Tacot2009/WETI-2025_26-Szymon_Filipkowski/.no-git_prezentacja/adc/496627323_1738310480376580_9046649333481038112_n.jpg

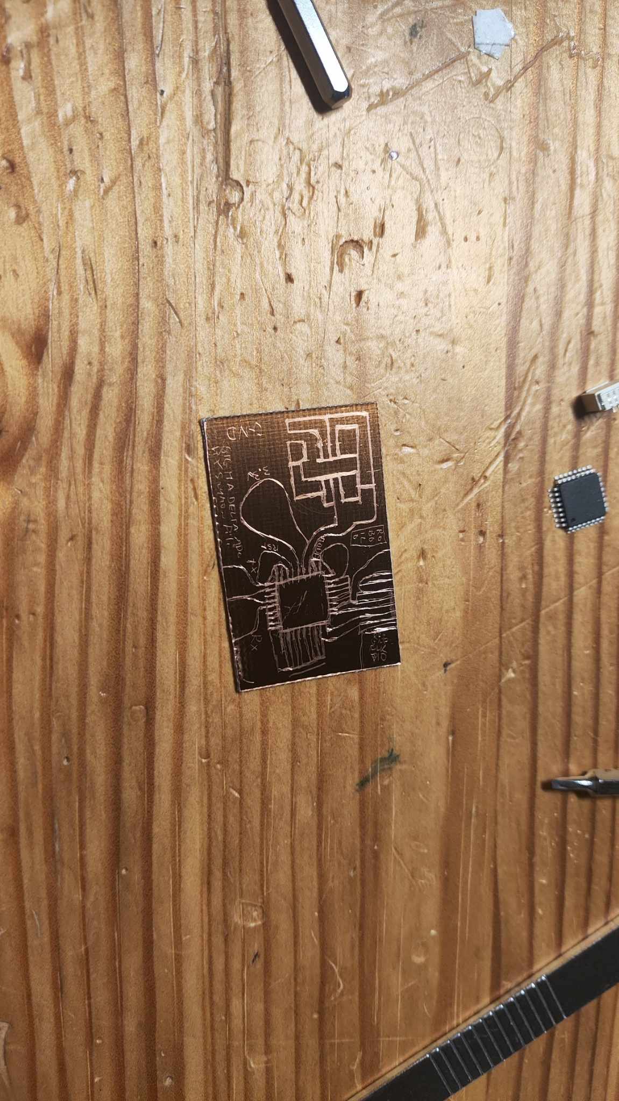
.no-git_prezentacja/adc/496627323_1738310480376580_9046649333481038112_n.jpg
