Tacot2009/WETI-2025_26-Szymon_Filipkowski/.no-git_prezentacja/adc/503926375_3727567250866873_8465031309394461046_n.jpg

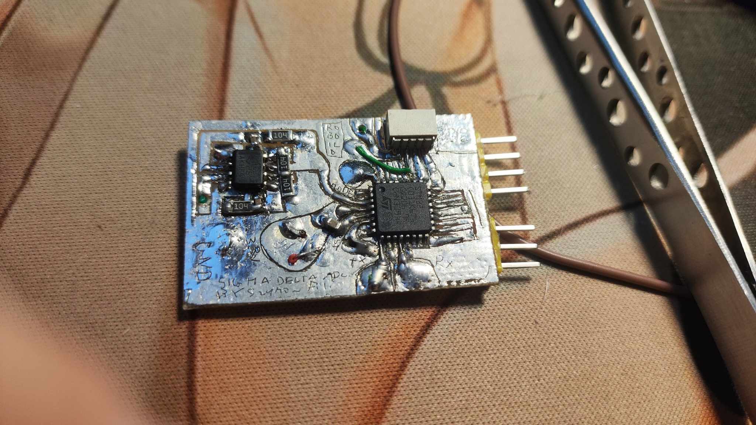
.no-git_prezentacja/adc/503926375_3727567250866873_8465031309394461046_n.jpg
