Tacot2009/WETI-2025_26-Szymon_Filipkowski/.no-git_prezentacja/adc/IMG_20250626_213812.jpg

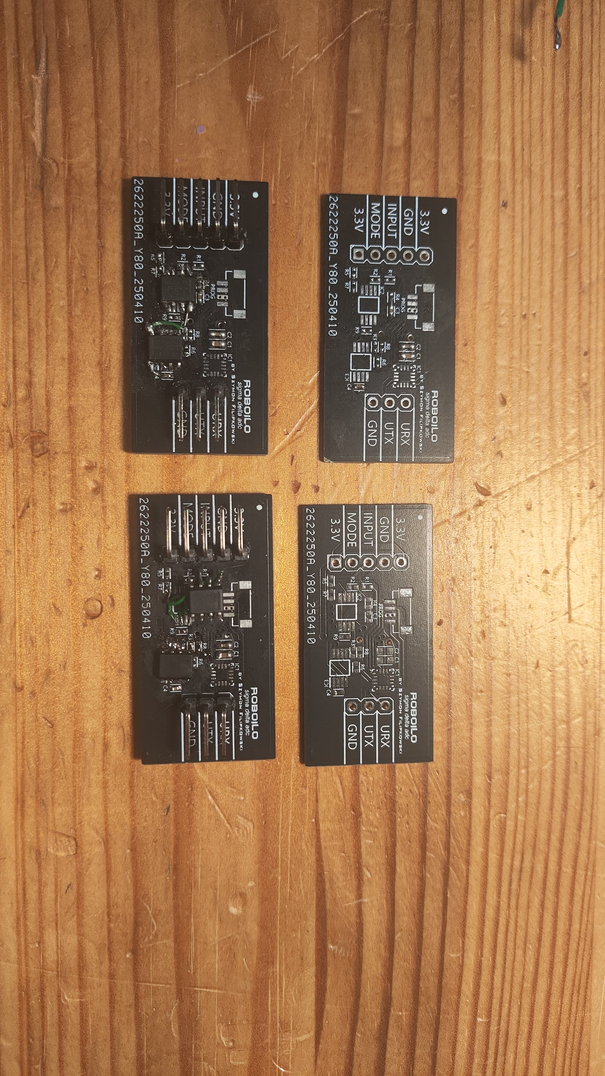
.no-git_prezentacja/adc/IMG_20250626_213812.jpg
