Tacot2009/WETI-2025_26-Szymon_Filipkowski/.no-git_prezentacja/adc/Screenshot 2025-06-26 221227.png

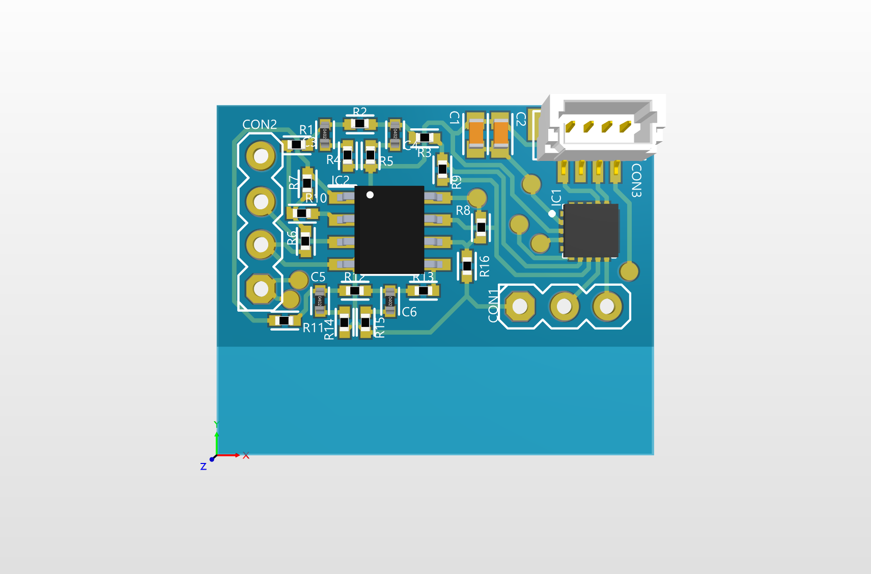
.no-git_prezentacja/adc/Screenshot 2025-06-26 221227.png
