Tacot2009/WETI-2025_26-Szymon_Filipkowski/.no-git_prezentacja/IMG_20250225_163824.jpg

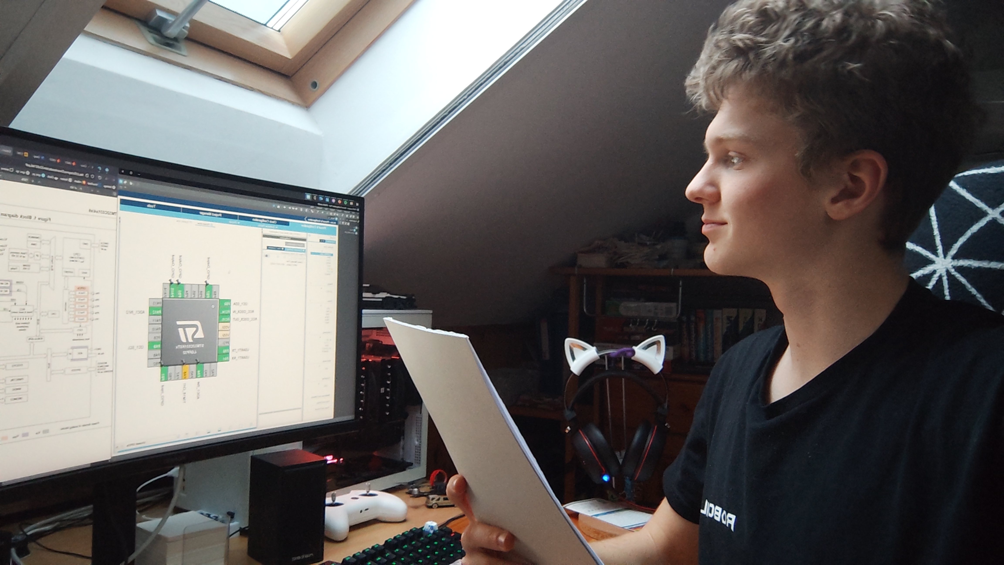
.no-git_prezentacja/IMG_20250225_163824.jpg
