Tacot2009/WETI-2025_26-Szymon_Filipkowski/.no-git_prezentacja/scheme z wartosciami.png

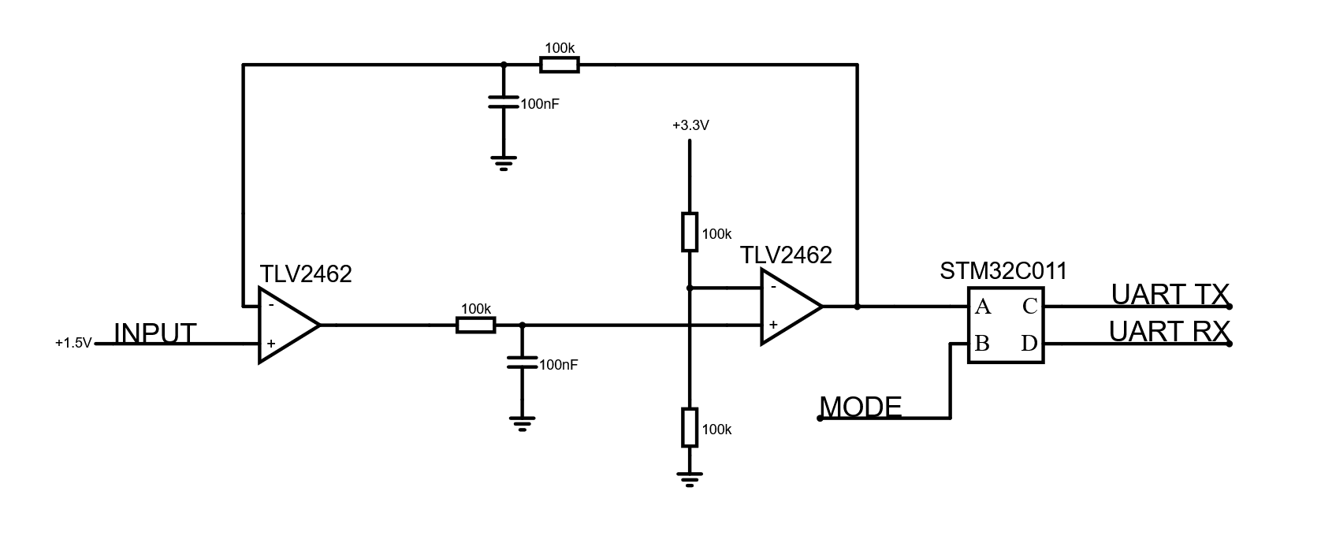
.no-git_prezentacja/scheme z wartosciami.png
