Tacot2009/WETI-2025_26-Szymon_Filipkowski/.no-git_prezentacja/Screenshot 2025-06-26 2114249.png

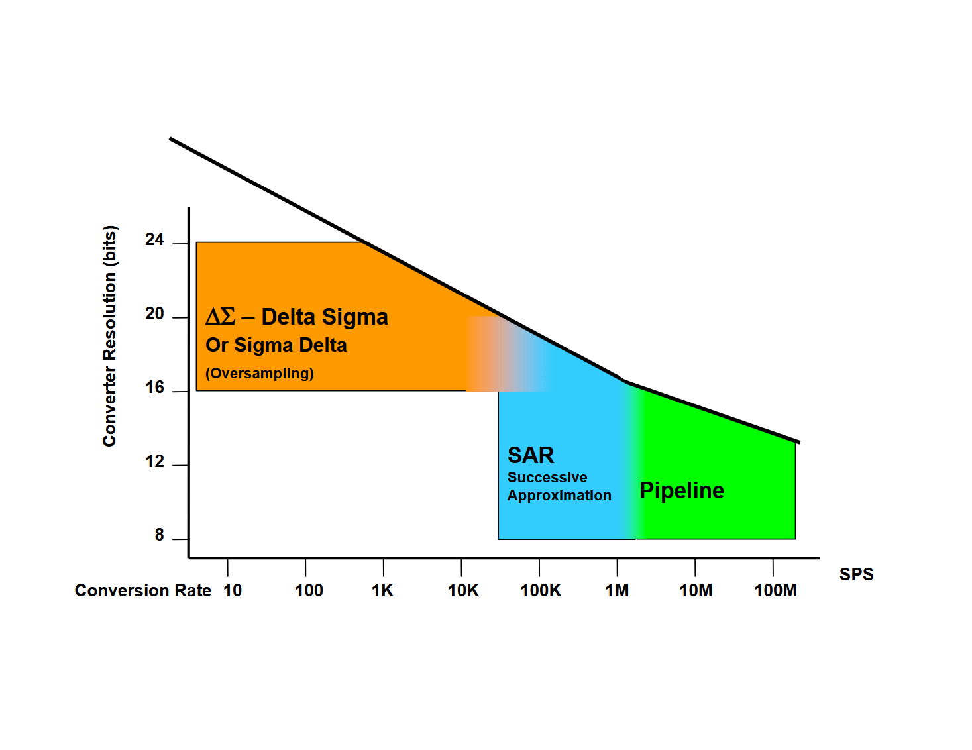
.no-git_prezentacja/Screenshot 2025-06-26 2114249.png
