Tacot2009/WETI-2025_26-Szymon_Filipkowski/.no-git_prezentacja/Screenshot 2025-06-29 230332.png

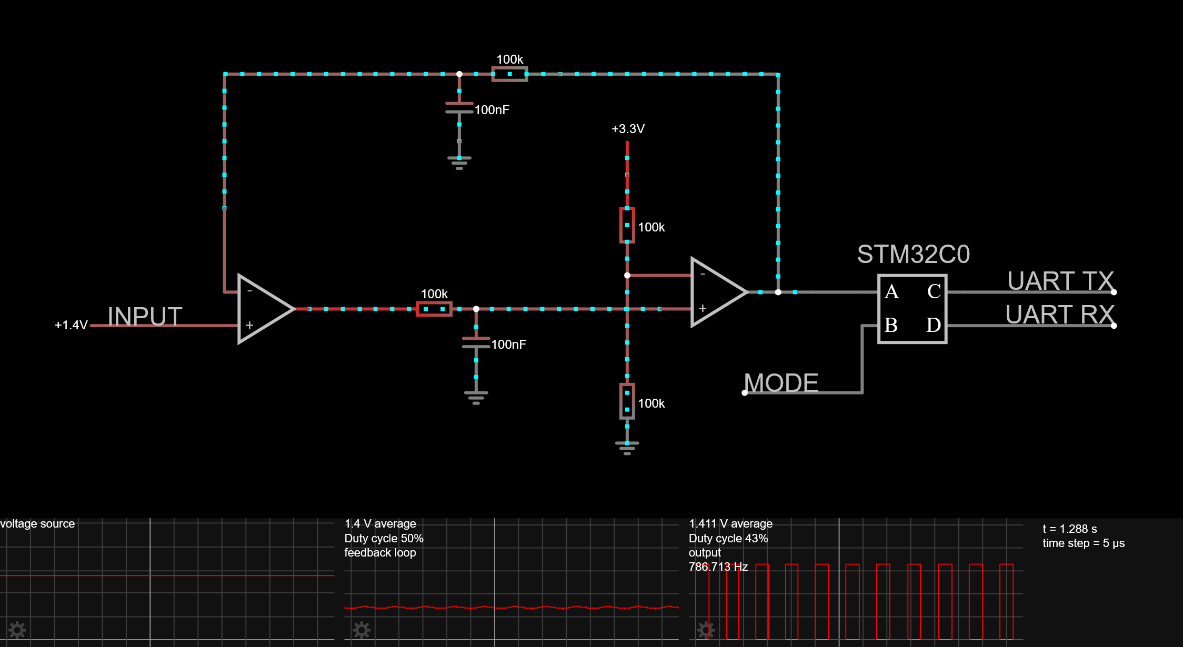
.no-git_prezentacja/Screenshot 2025-06-29 230332.png
