Tacot2009/WETI-2025_26-Szymon_Filipkowski/.no-git_prezentacja/texas/Screenshot 2025-06-25 181031.png

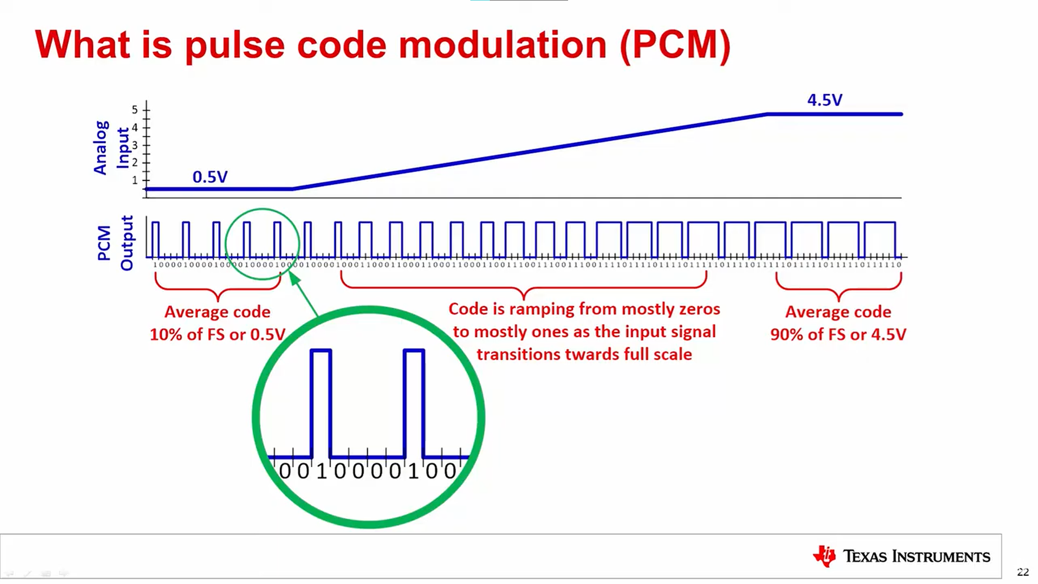
.no-git_prezentacja/texas/Screenshot 2025-06-25 181031.png
